marsairforce/reverb_tank/v3/pictures/0.jpg

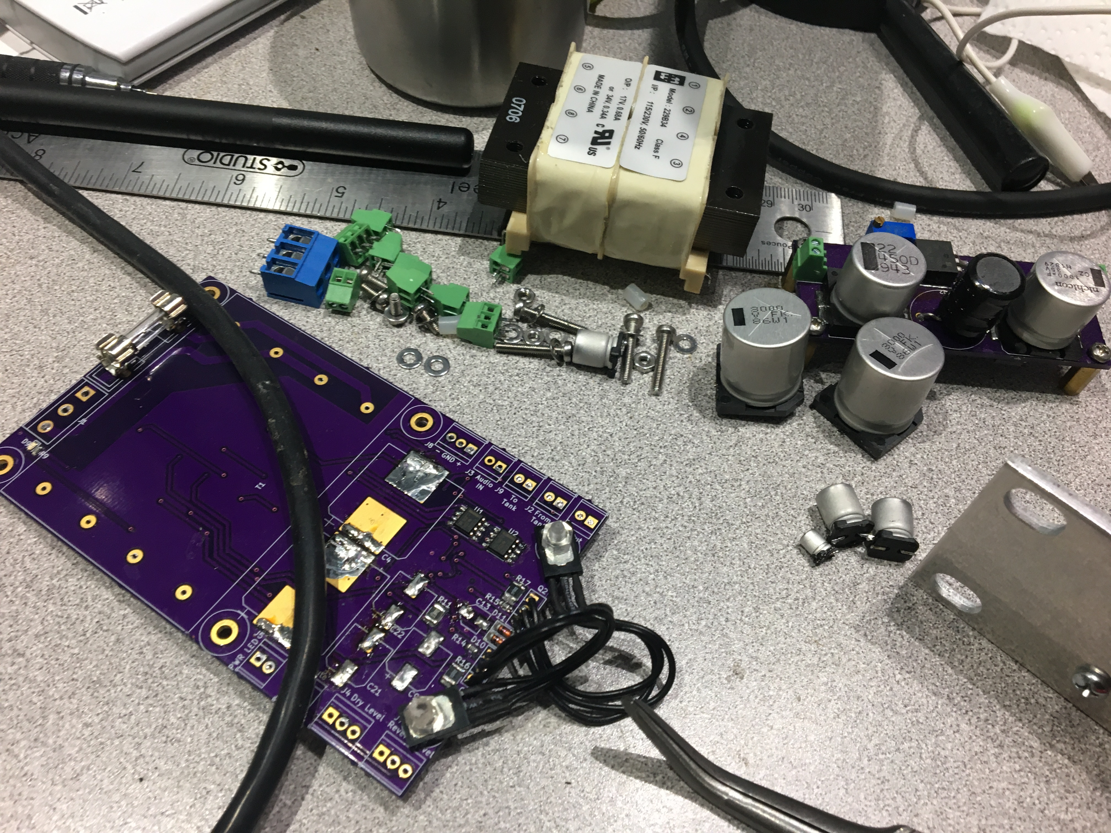
v3/pictures/0.jpg
