marsairforce/reverb_tank/v3/pictures/2.jpg

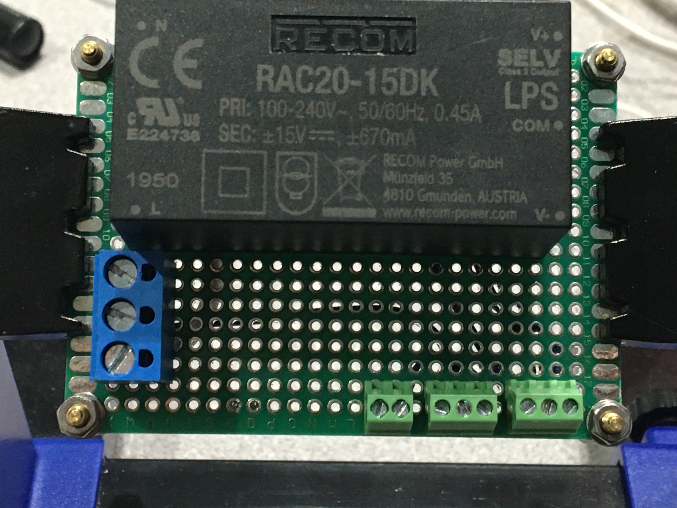
v3/pictures/2.jpg
