marsairforce/reverb_tank/v3/pictures/3.jpg

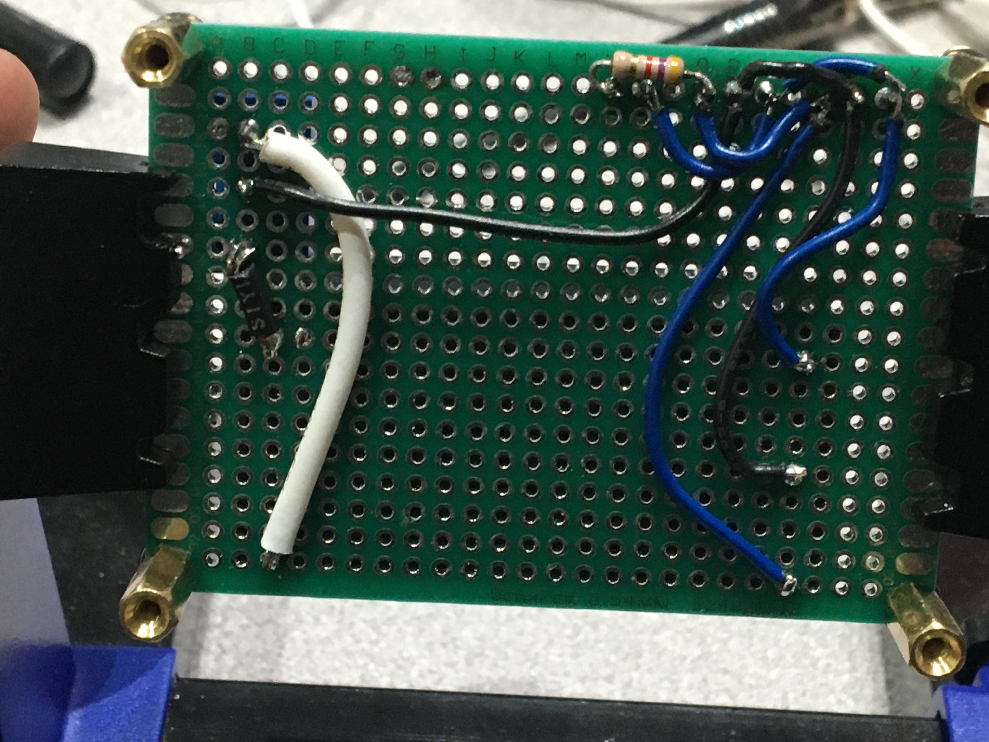
v3/pictures/3.jpg
