marsairforce/reverb_tank/v3/pictures/4.jpg

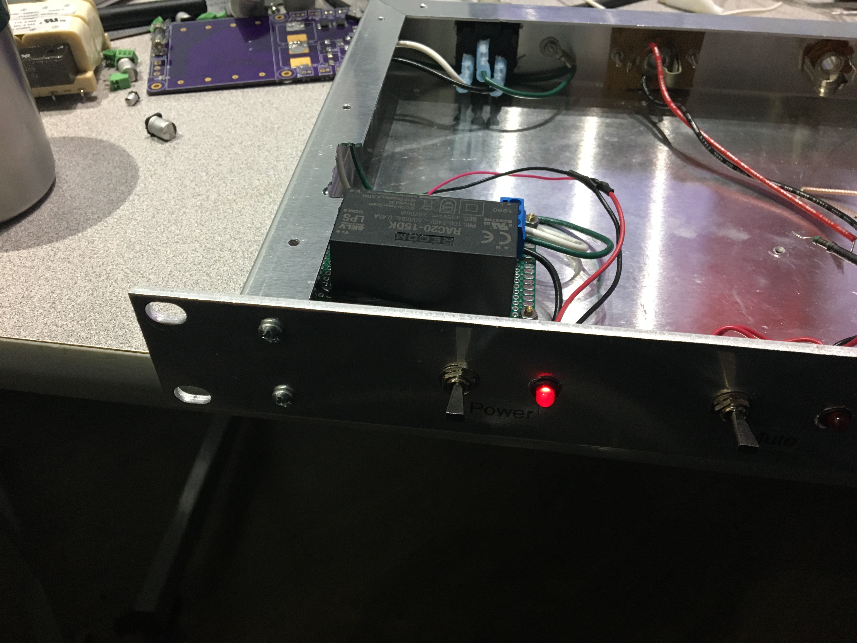
v3/pictures/4.jpg
