marsairforce/reverb_tank/v3/pictures/6.jpg

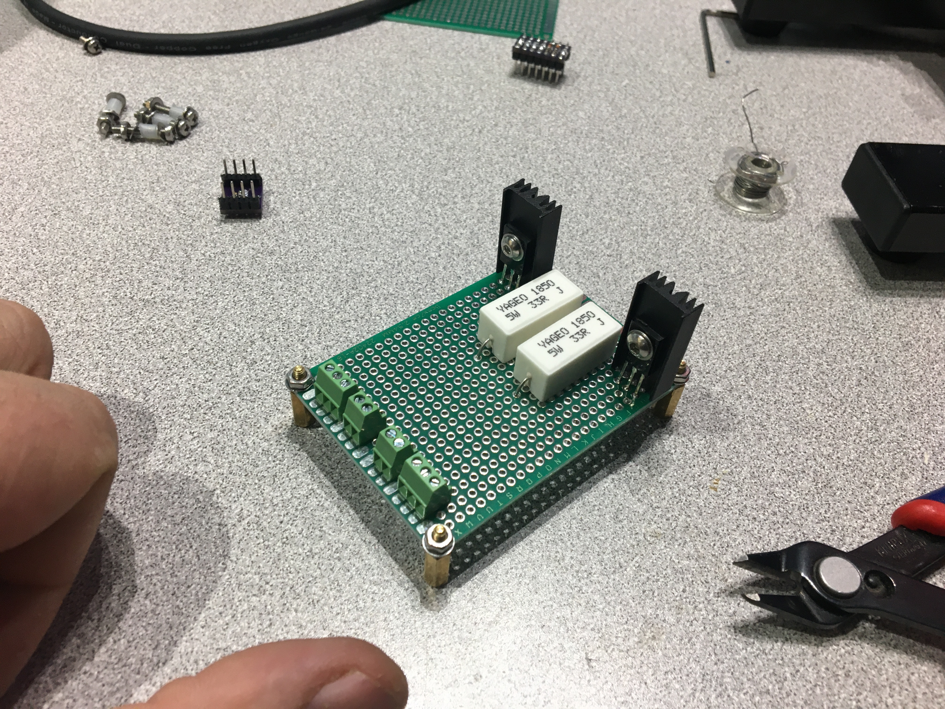
v3/pictures/6.jpg
