marsairforce/reverb_tank/v3/pictures/7.jpg

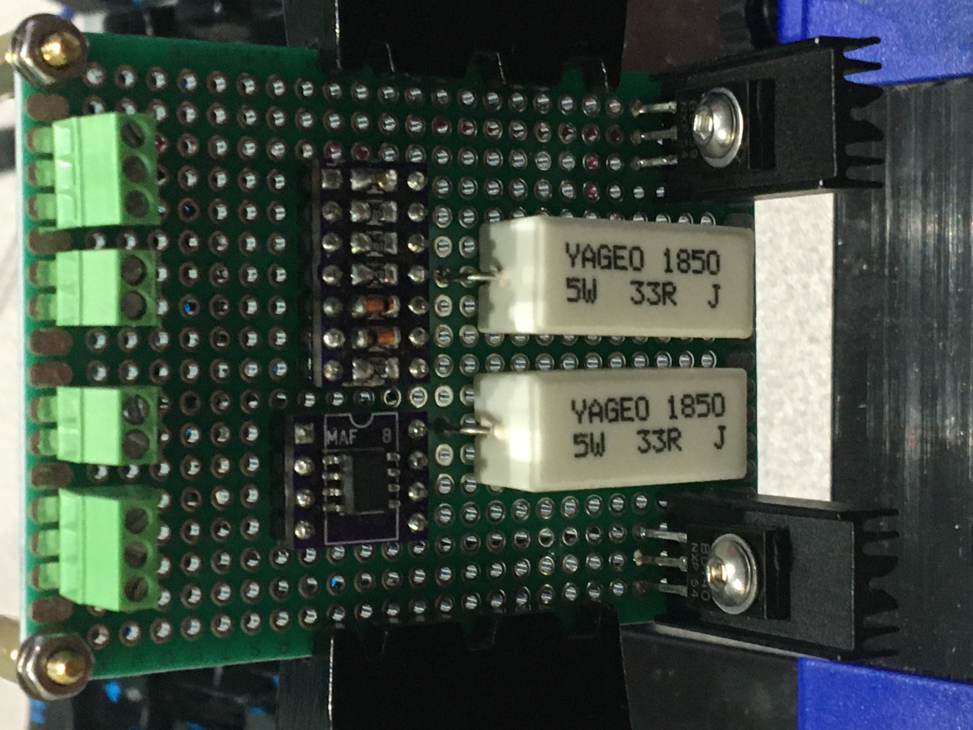
v3/pictures/7.jpg
