marsairforce/reverb_tank/v3/pictures/8.jpg

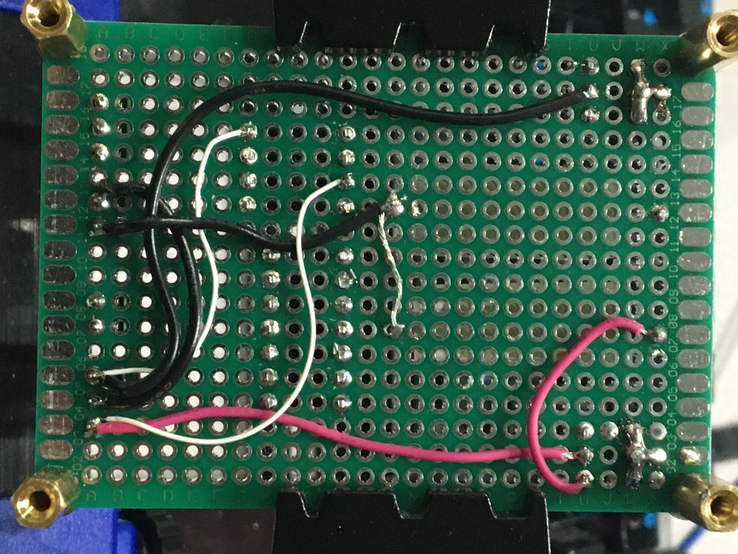
v3/pictures/8.jpg
