marsairforce/reverb_tank/v3/pictures/9.jpg

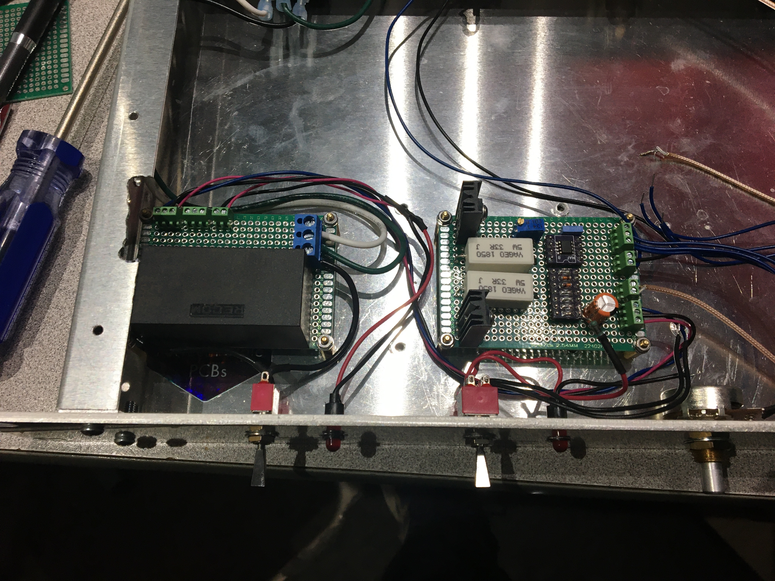
v3/pictures/9.jpg
