marsairforce/reverb_tank/v3/pictures/11.jpg

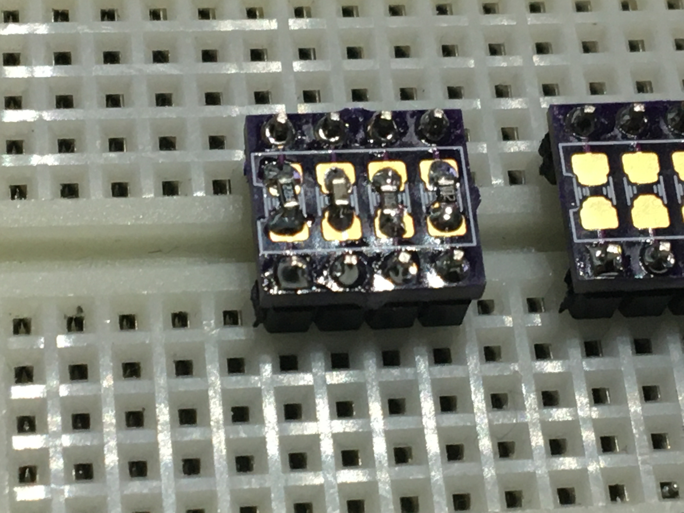
v3/pictures/11.jpg
