marsairforce/reverb_tank/v3/pictures/12.jpg

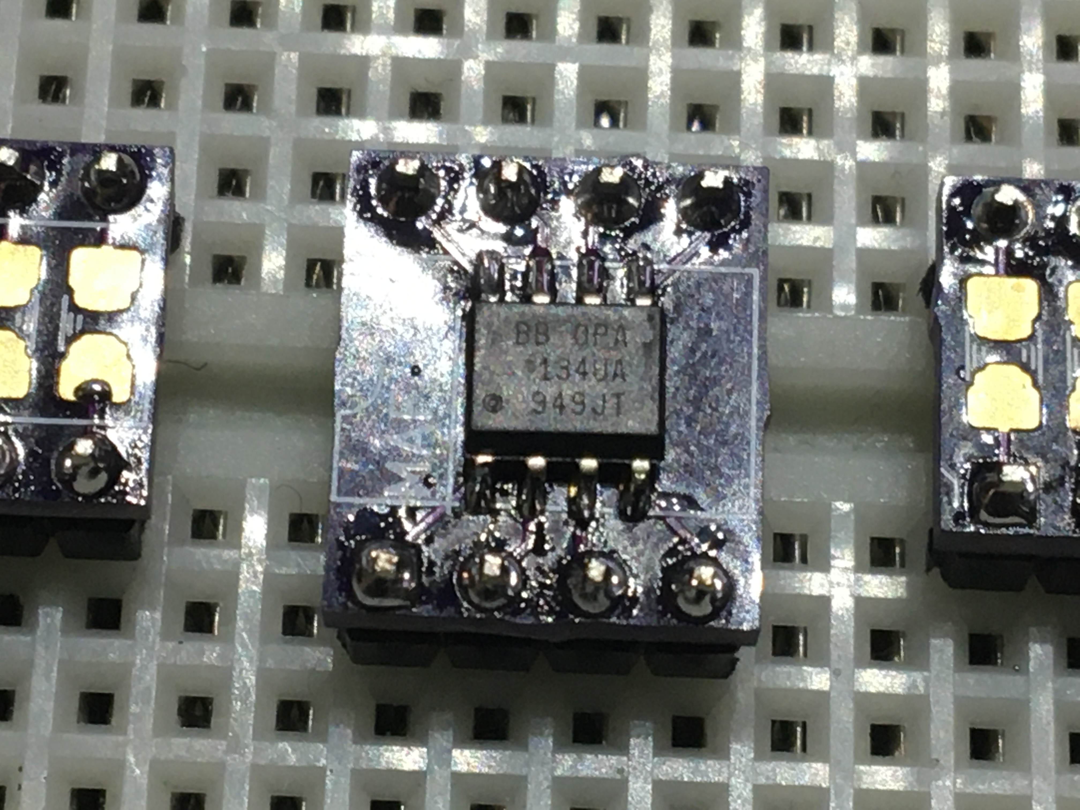
v3/pictures/12.jpg
