marsairforce/reverb_tank/v3/pictures/13.jpg

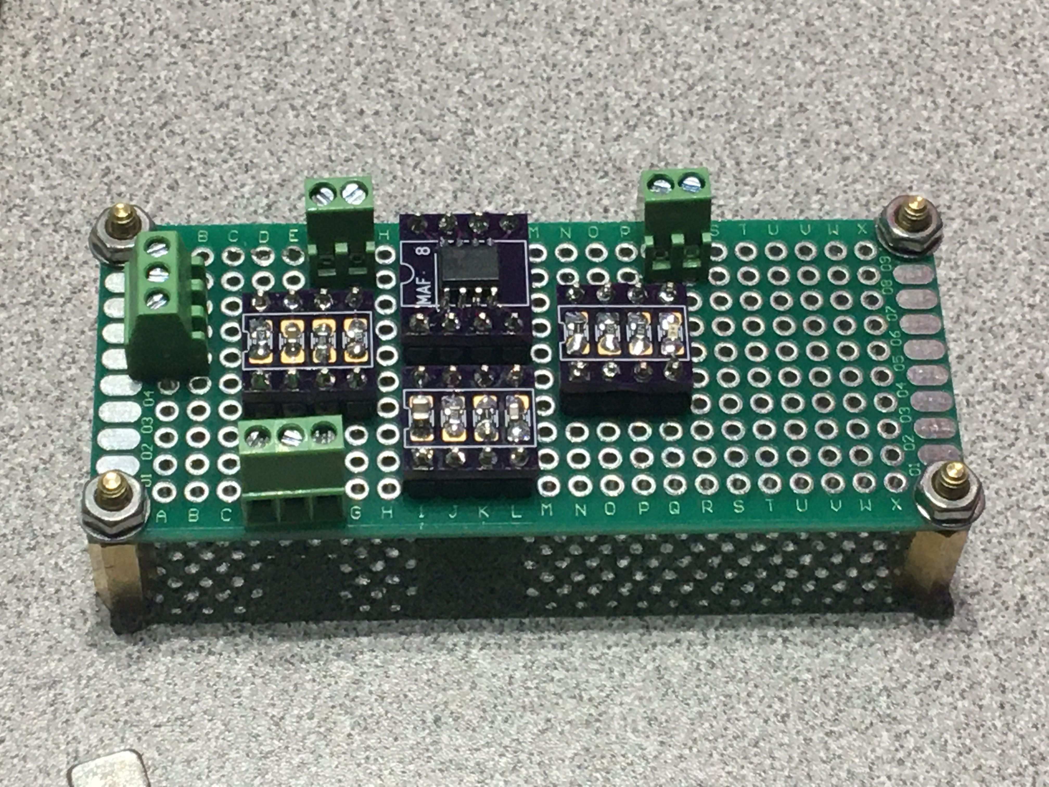
v3/pictures/13.jpg
