marsairforce/reverb_tank/v3/pictures/14.jpg

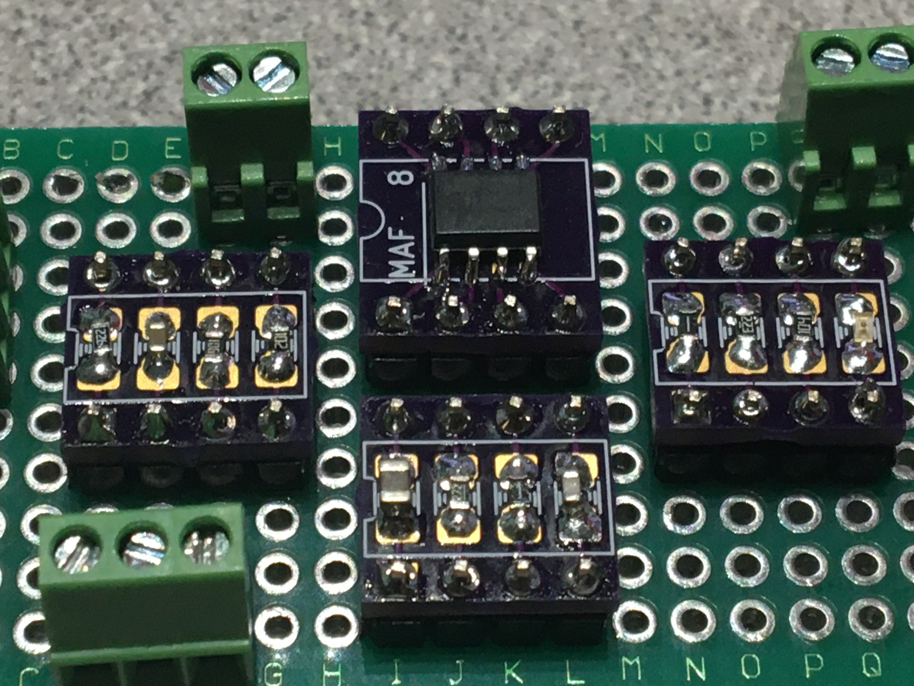
v3/pictures/14.jpg
