marsairforce/reverb_tank/v3/pictures/15.jpg

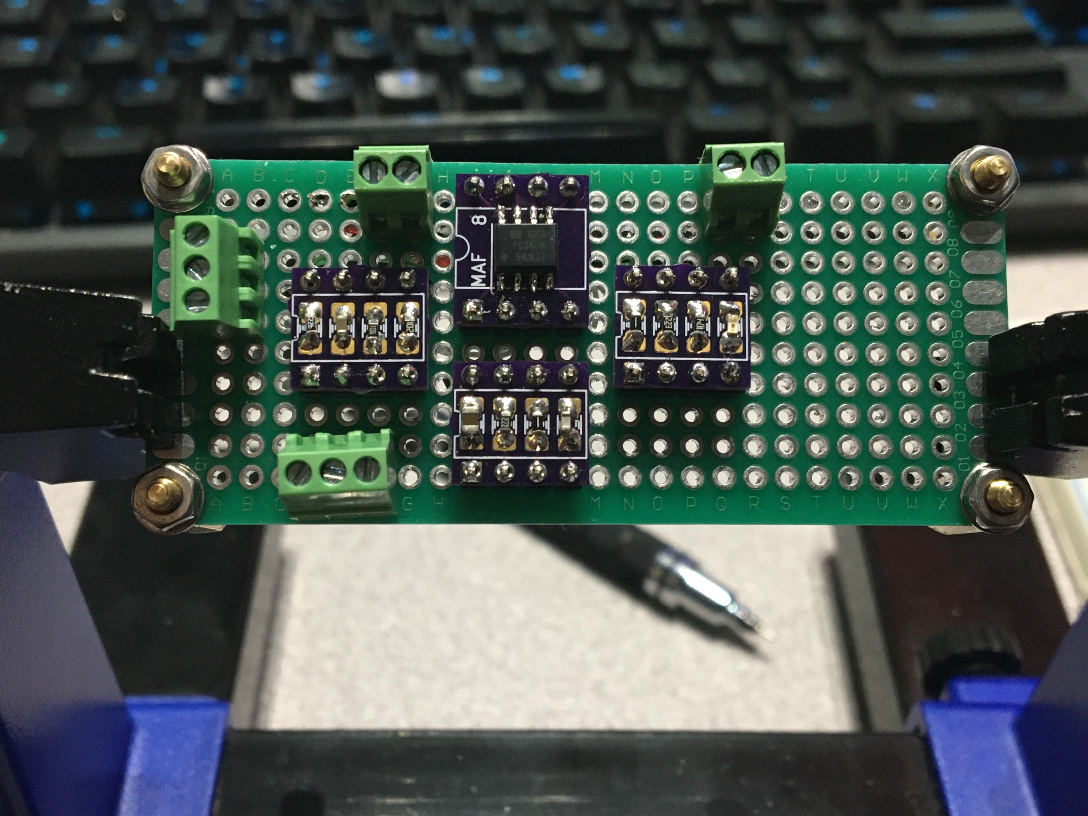
v3/pictures/15.jpg
