marsairforce/reverb_tank/v3/pictures/16.jpg

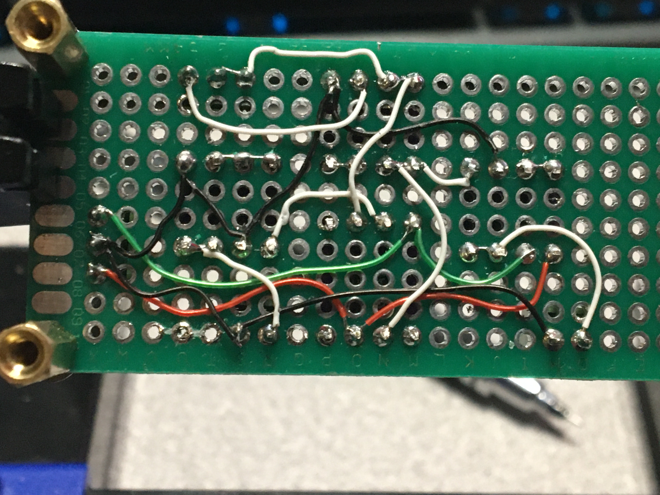
v3/pictures/16.jpg
